blackbox114/Blacky/3Dprint/raspberry pad H.stl

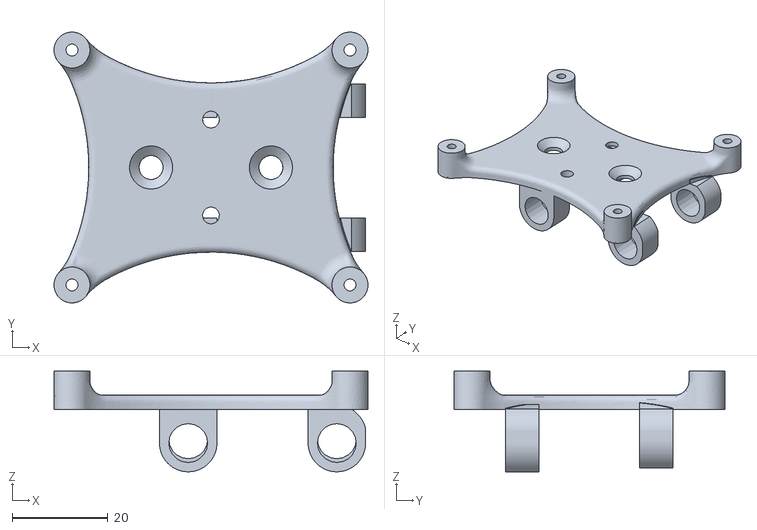
[picture p26: CAD file, 2020-05-13]
3Dprint/raspberry pad H.stl
65.5 x 56.5 x 21.0
