blackbox114/Blacky/3Dprint/HipOutsideFDM.stl

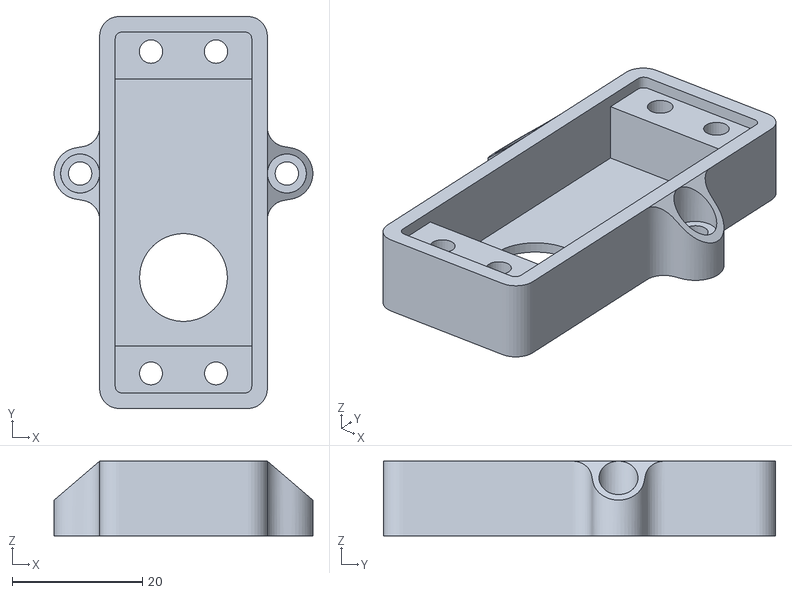
[picture p27: CAD file, 2020-05-11]
3Dprint/HipOutsideFDM.stl
39.8 x 60.3 x 11.5
