blackbox114/Blacky/3Dprint/HipInsideFDM.stl

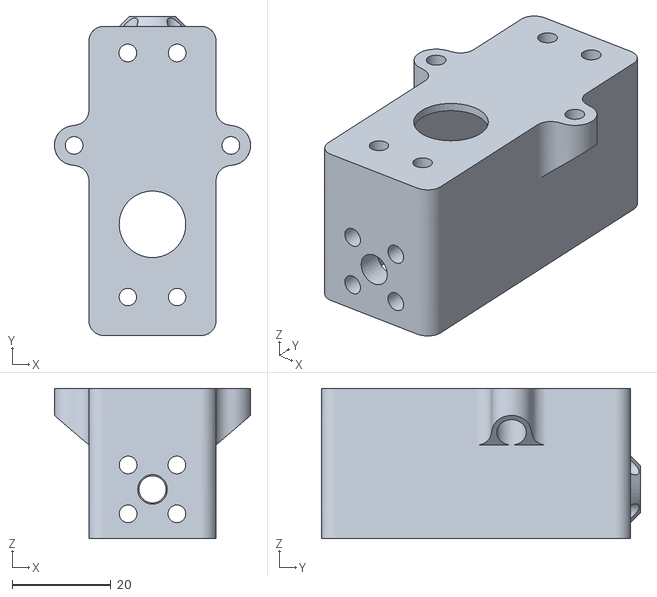
[picture p28: CAD file, 2020-05-11]
3Dprint/HipInsideFDM.stl
39.8 x 64.7 x 30.5
