blackbox114/Blacky/3Dprint/screw-back-back.stl

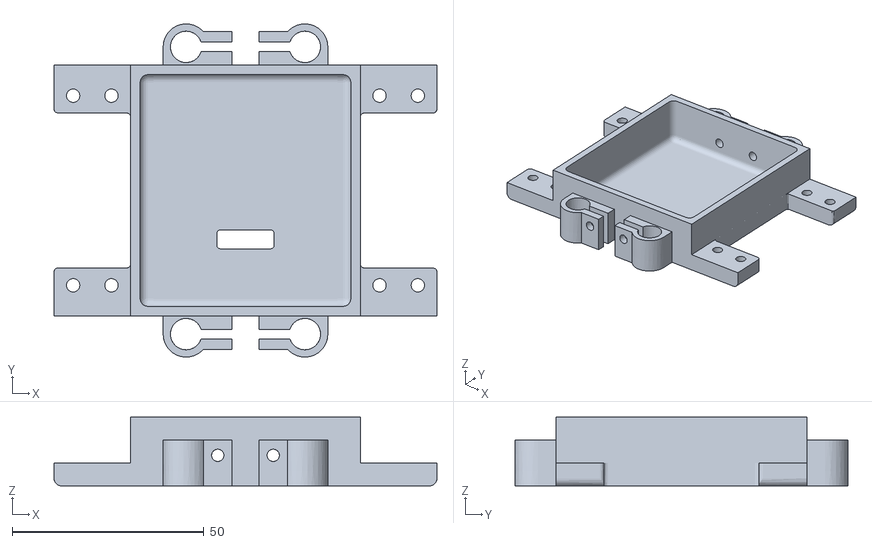
[picture p29: CAD file, 2021-06-06]
3Dprint/screw-back-back.stl
100.0 x 87.0 x 18.0
